b1uN7/DEFCON-26-Flying-Skull-Badge/Resources/2.4-LCD-Module-2.jpg

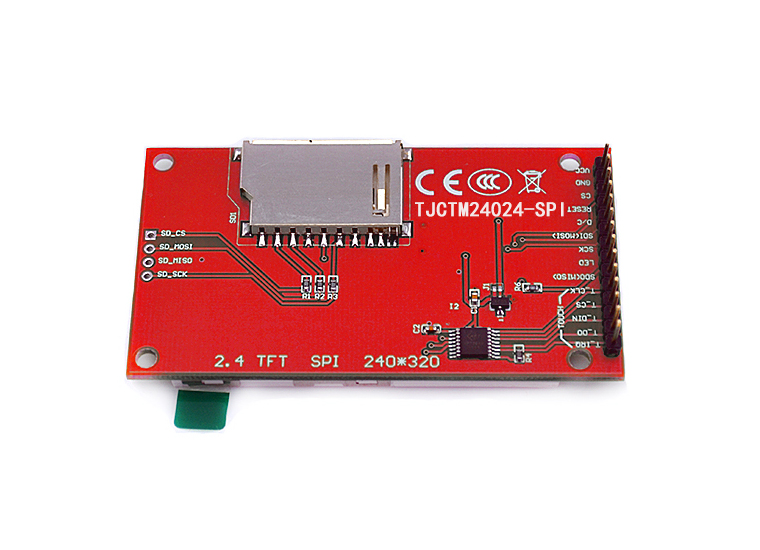
Resources/2.4-LCD-Module-2.jpg
