b1uN7/DEFCON-26-Flying-Skull-Badge/Addon_board/images/Famale header Connector High Reliability Socket 2.0mm Pitch 18pin SMD SMM 118 02 S S K TR-in Connectors from Lights & Lighting … 2018-07-03 07-32-30.jpg

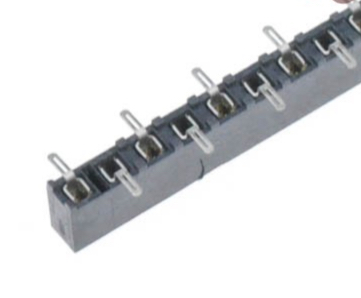
Addon_board/images/Famale header Connector High Reliability Socket 2.0mm Pitch 18pin SMD SMM 118 02 S S K TR-in Connectors from Lights & Lighting … 2018-07-03 07-32-30.jpg
