b1uN7/DEFCON-26-Flying-Skull-Badge/Addon_board/images/longStackable.jpg

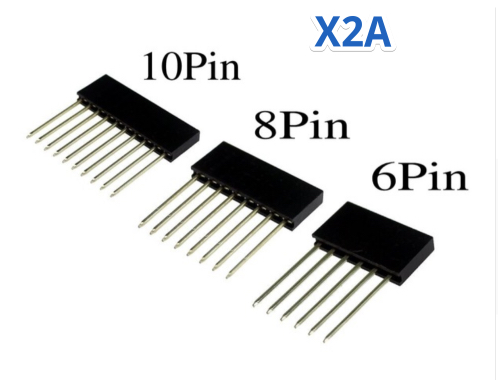
Addon_board/images/longStackable.jpg
