b1uN7/DEFCON-26-Flying-Skull-Badge/Code/LEONARDOpins.jpg

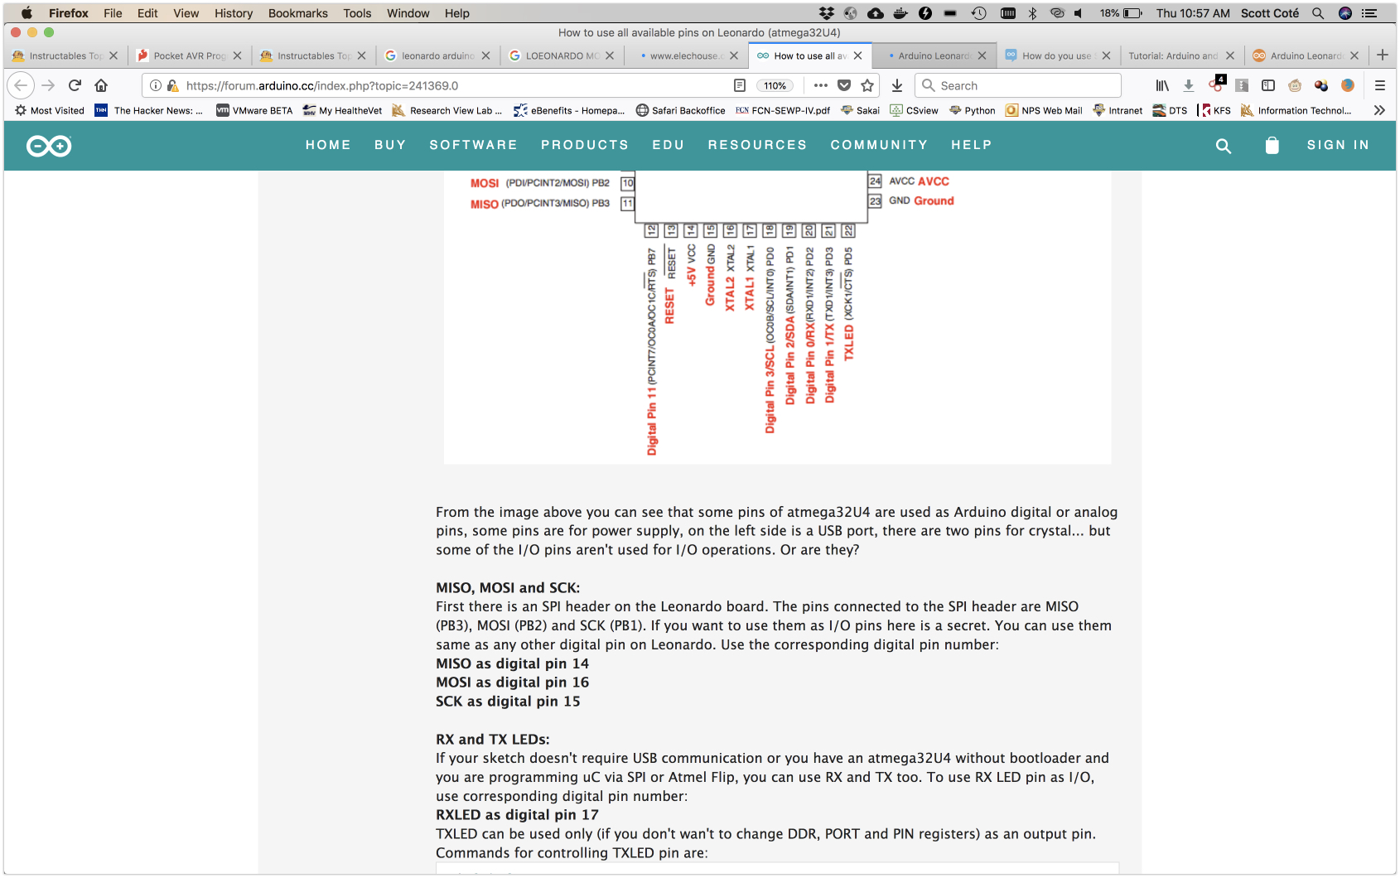
Code/LEONARDOpins.jpg
