b1uN7/DEFCON-26-Flying-Skull-Badge/FlightControlUnitBoard V3/graphics/solidheart.jpg

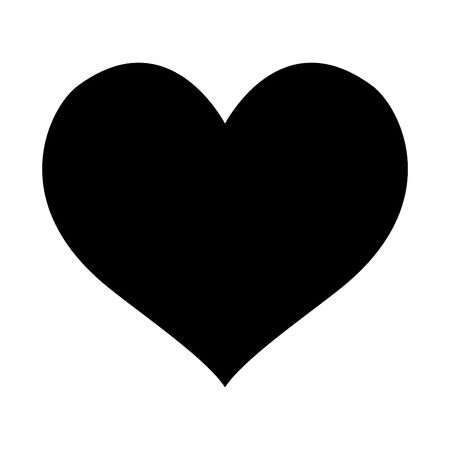
FlightControlUnitBoard V3/graphics/solidheart.jpg
