b1uN7/DEFCON-26-Flying-Skull-Badge/FlightControlUnitBoard V3/graphics/think-line-heart-outline-hi.png

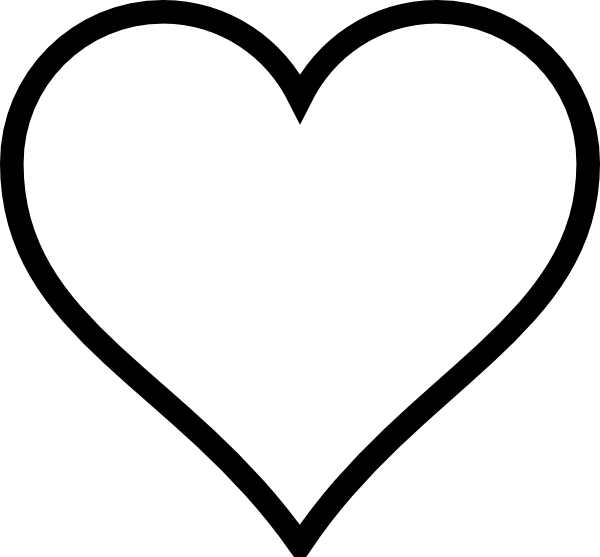
FlightControlUnitBoard V3/graphics/think-line-heart-outline-hi.png
